eez-open/dib-dcm224/Images/EEZ_DIB_DCM224_PCB_parts_top.png

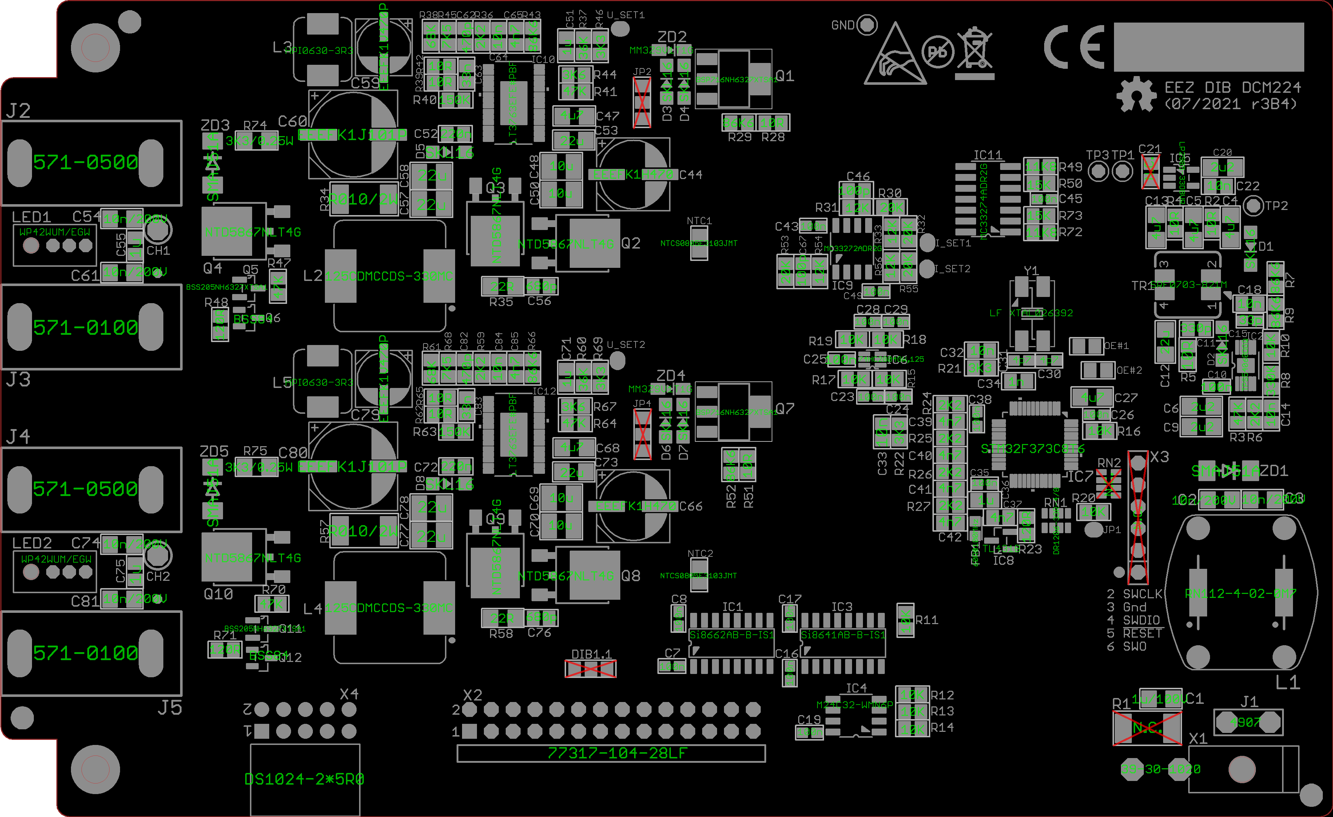
Images/EEZ_DIB_DCM224_PCB_parts_top.png
